nessuno7/Rubik-s-cube-solving-machine/CFOP_algorithm/images/color_array_1.jpg

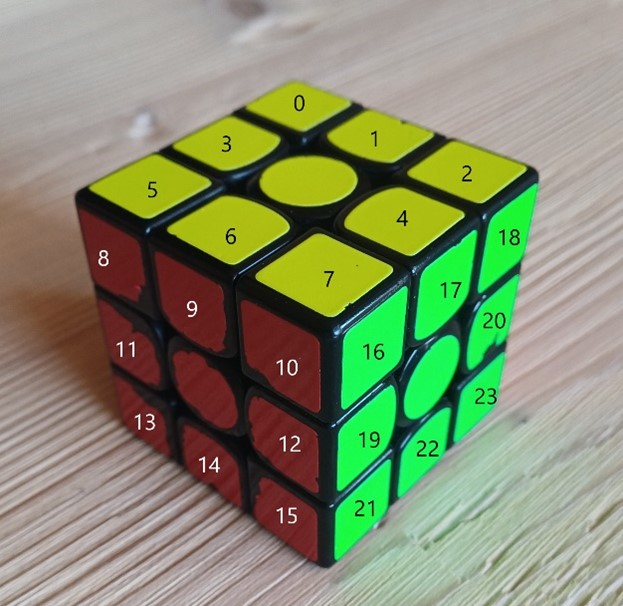
CFOP_algorithm/images/color_array_1.jpg
