nessuno7/Rubik-s-cube-solving-machine/CFOP_algorithm/images/edge_positions_1.jpg

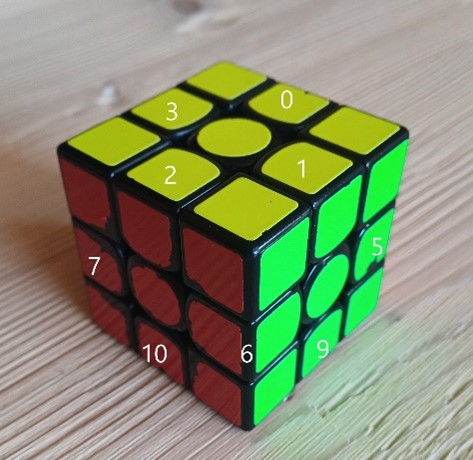
CFOP_algorithm/images/edge_positions_1.jpg
