nessuno7/Rubik-s-cube-solving-machine/CFOP_algorithm/images/move_notation_2.jpg

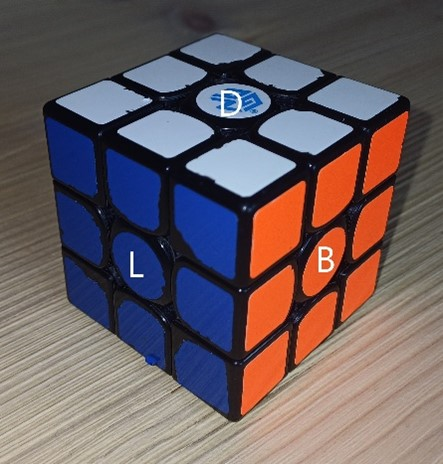
CFOP_algorithm/images/move_notation_2.jpg
